Good-Great-Grand-Wonderful/crosses/models/experiments/adjustable/adjustable-matrix-mount-right.step

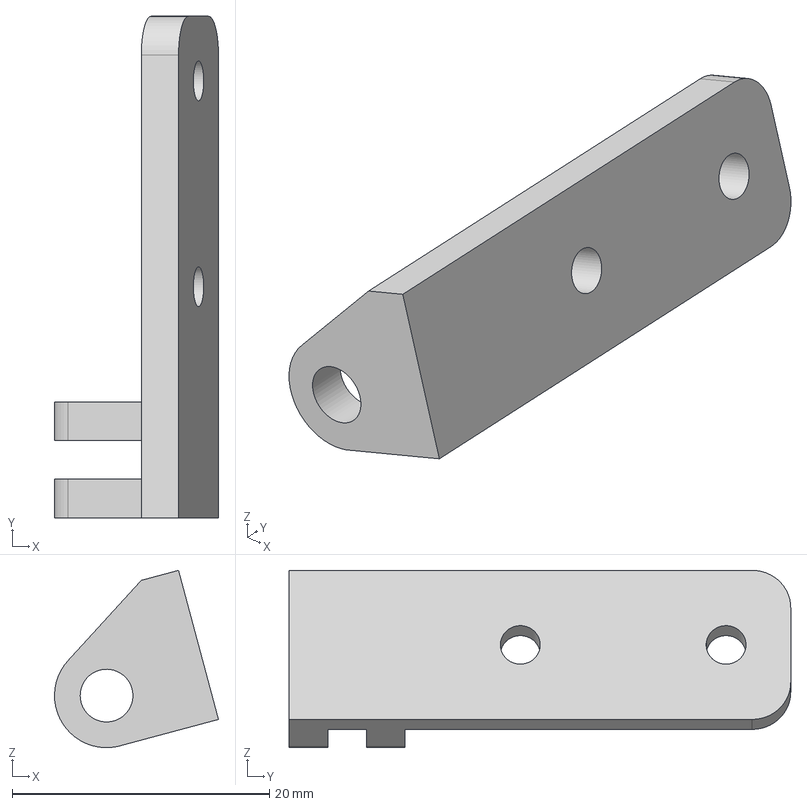
[picture p15: CAD file, 2026-01-19]
models/experiments/adjustable/adjustable-matrix-mount-right.step
12.8 x 39.0 x 13.8 mm
