Good-Great-Grand-Wonderful/crosses/models/experiments/adjustable/adjustable-matrix-42-right.step

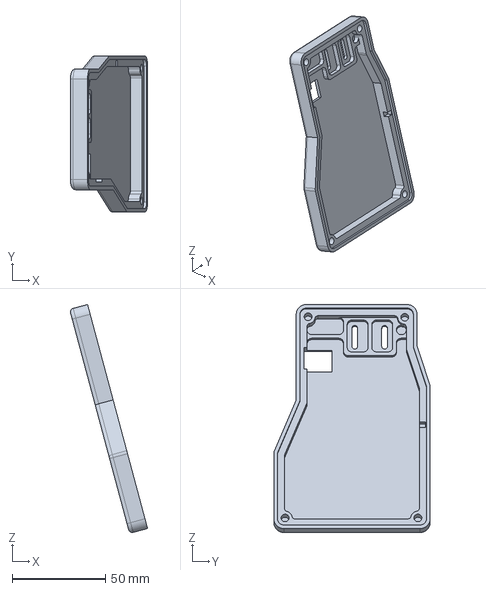
[picture p16: CAD file, 2026-01-19]
models/experiments/adjustable/adjustable-matrix-42-right.step
41.4 x 83.8 x 122.2 mm
