Good-Great-Grand-Wonderful/crosses/models/thumbs/Crosses-Trackball-Mount-Left.step

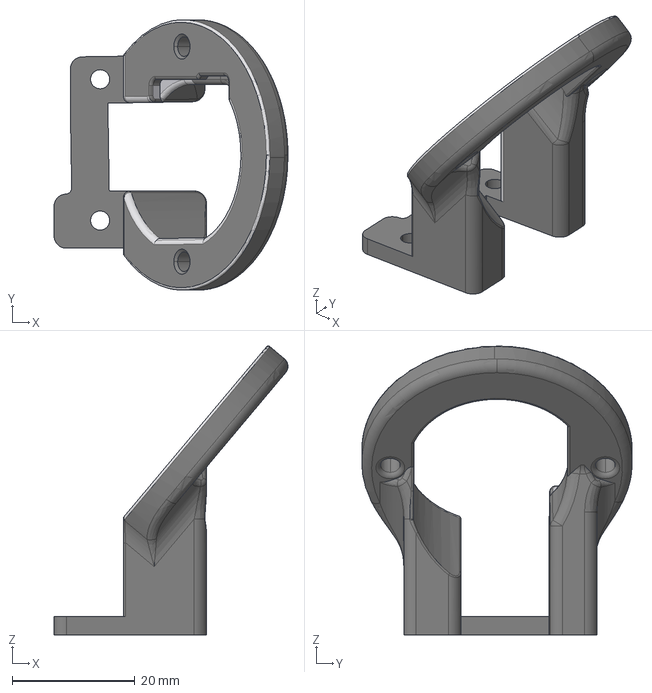
[picture p17: CAD file, 2025-11-24]
models/thumbs/Crosses-Trackball-Mount-Left.step
38.1 x 44.0 x 47.0 mm
