Good-Great-Grand-Wonderful/crosses/models/experiments/adjustable/adjustable-trackball-mount-right.step

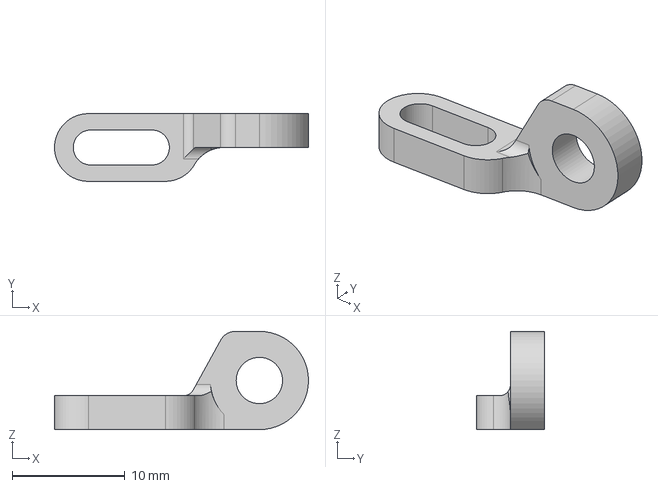
[picture p18: CAD file, 2026-01-19]
models/experiments/adjustable/adjustable-trackball-mount-right.step
22.5 x 6.00 x 8.70 mm
