Good-Great-Grand-Wonderful/crosses/models/thumbs/Bridges-Trackball-Mount-Left.step

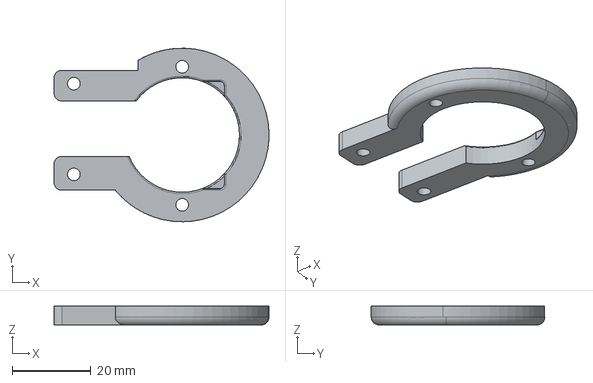
[picture p19: CAD file, 2025-11-24]
models/thumbs/Bridges-Trackball-Mount-Left.step
54.5 x 44.0 x 4.80 mm
